PavlenkoG/ECP5_PCIE_Analyzer/fpga_logic/src/pcs_pci_rx.vhd

--
-- Verific VHDL Description of module DCUA
--

-- DCUA is a black-box. Cannot print a valid VHDL entity description for it

--
-- Verific VHDL Description of module pcs_pci_rx
--

library ieee ;
use ieee.std_logic_1164.all ;

library ecp5um ;
use ecp5um.components.all ;

entity pcs_pci_rx is
    port (hdinp: in std_logic;
        hdinn: in std_logic;
        rxrefclk: in std_logic;
        rx_pclk: out std_logic;
        rxdata: out std_logic_vector(7 downto 0);
        rx_k: out std_logic_vector(0 downto 0);
        rxstatus0: out std_logic_vector(2 downto 0);
        pcie_det_en_c: in std_logic;
        pcie_ct_c: in std_logic;
        signal_detect_c: in std_logic;
        pcie_done_s: out std_logic;
        pcie_con_s: out std_logic;
        rx_los_low_s: out std_logic;
        lsm_status_s: out std_logic;
        rx_cdr_lol_s: out std_logic;
        rx_pcs_rst_c: in std_logic;
        rx_serdes_rst_c: in std_logic;
        rx_pwrup_c: in std_logic;
        rst_dual_c: in std_logic;
        serdes_rst_dual_c: in std_logic;
        serdes_pdb: in std_logic
    );
    
end entity pcs_pci_rx;

architecture v1 of pcs_pci_rx is 
    signal n40,n39,n1,n2,n3,n4,rx_pclk_c,n5,n6,n7,n8,n9,n10,n11,
        n12,n13,n14,n15,n16,n17,n18,n19,n20,n21,n22,n23,n24,n25,
        n26,n27,n28,n29,n30,n31,n32,n33,n34,n35,n36,n37,n38,n41,
        gnd,pwr,n42,n43,n44,n45,n46,n47,n48,n49,n50,n51,n52,n53,
        n54,n55,n56,n57,n58,n59,n60,n61,n62,n63,n64,n65,n66,n67,
        n68,n69,n70,n71,n72,n73,n74,n75,n76,n77,n78,n79,n80,n81,
        n82,n83,n84,n85,n86,n87,n88,n89,n90,n91,n92,n93,n94,n95,
        n96,n97,n98,n99,n100,n101,n102,n103,n104,n105,n106,n107,
        n108,n109,n110,n111,n112,n113,\_Z\ : std_logic; 
    attribute LOC : string;
    attribute LOC of DCU1_inst : label is "DCU1";
    attribute CHAN : string;
    attribute CHAN of DCU1_inst : label is "CH0";
begin
    rx_pclk <= rx_pclk_c;
    DCU1_inst: component DCUA generic map (D_MACROPDB=>"0b1",D_IB_PWDNB=>"0b1",
        D_XGE_MODE=>"0b0",D_LOW_MARK=>"0d4",D_HIGH_MARK=>"0d12",D_BUS8BIT_SEL=>"0b0",
        D_CDR_LOL_SET=>"0b00",D_TXPLL_PWDNB=>"0b1",CH0_UC_MODE=>"0b0",CH0_PCIE_MODE=>"0b1",
        CH0_RIO_MODE=>"0b0",CH0_WA_MODE=>"0b0",CH0_INVERT_RX=>"0b1",CH0_INVERT_TX=>"0b0",
        CH0_PRBS_SELECTION=>"0b0",CH0_GE_AN_ENABLE=>"0b0",CH0_PRBS_LOCK=>"0b0",
        CH0_PRBS_ENABLE=>"0b0",CH0_ENABLE_CG_ALIGN=>"0b1",CH0_TX_GEAR_MODE=>"0b1",
        CH0_RX_GEAR_MODE=>"0b0",CH0_PCS_DET_TIME_SEL=>"0b00",CH0_PCIE_EI_EN=>"0b0",
        CH0_TX_GEAR_BYPASS=>"0b0",CH0_ENC_BYPASS=>"0b0",CH0_SB_BYPASS=>"0b0",
        CH0_RX_SB_BYPASS=>"0b1",CH0_WA_BYPASS=>"0b0",CH0_DEC_BYPASS=>"0b0",
        CH0_CTC_BYPASS=>"0b1",CH0_RX_GEAR_BYPASS=>"0b0",CH0_LSM_DISABLE=>"0b0",
        CH0_MATCH_2_ENABLE=>"0b0",CH0_MATCH_4_ENABLE=>"0b1",CH0_MIN_IPG_CNT=>"0b11",
        CH0_CC_MATCH_1=>"0x1BC",CH0_CC_MATCH_2=>"0x11C",CH0_CC_MATCH_3=>"0x11C",
        CH0_CC_MATCH_4=>"0x11C",CH0_UDF_COMMA_MASK=>"0x3ff",CH0_UDF_COMMA_A=>"0x283",
        CH0_UDF_COMMA_B=>"0x17C",CH0_RX_DCO_CK_DIV=>"0b000",CH0_RCV_DCC_EN=>"0b0",
        CH0_TPWDNB=>"0b0",CH0_RATE_MODE_TX=>"0b0",CH0_RTERM_TX=>"0d19",CH0_TX_CM_SEL=>"0b00",
        CH0_TDRV_PRE_EN=>"0b0",CH0_TDRV_SLICE0_SEL=>"0b00",CH0_TDRV_SLICE1_SEL=>"0b00",
        CH0_TDRV_SLICE2_SEL=>"0b00",CH0_TDRV_SLICE3_SEL=>"0b00",CH0_TDRV_SLICE4_SEL=>"0b00",
        CH0_TDRV_SLICE5_SEL=>"0b00",CH0_TDRV_SLICE0_CUR=>"0b000",CH0_TDRV_SLICE1_CUR=>"0b000",
        CH0_TDRV_SLICE2_CUR=>"0b00",CH0_TDRV_SLICE3_CUR=>"0b00",CH0_TDRV_SLICE4_CUR=>"0b00",
        CH0_TDRV_SLICE5_CUR=>"0b00",CH0_TDRV_DAT_SEL=>"0b00",CH0_TX_DIV11_SEL=>"0b0",
        CH0_RPWDNB=>"0b1",CH0_RATE_MODE_RX=>"0b0",CH0_RX_DIV11_SEL=>"0b0",
        CH0_SEL_SD_RX_CLK=>"0b1",CH0_FF_RX_H_CLK_EN=>"0b0",CH0_FF_RX_F_CLK_DIS=>"0b0",
        CH0_FF_TX_H_CLK_EN=>"0b1",CH0_FF_TX_F_CLK_DIS=>"0b1",CH0_TDRV_POST_EN=>"0b0",
        CH0_TX_POST_SIGN=>"0b0",CH0_TX_PRE_SIGN=>"0b0",CH0_REQ_LVL_SET=>"0b00",
        CH0_REQ_EN=>"0b0",CH0_RTERM_RX=>"0d22",CH0_RXTERM_CM=>"0b11",CH0_PDEN_SEL=>"0b1",
        CH0_RXIN_CM=>"0b11",CH0_LEQ_OFFSET_SEL=>"0b0",CH0_LEQ_OFFSET_TRIM=>"0b000",
        CH0_RLOS_SEL=>"0b1",CH0_RX_LOS_LVL=>"0b100",CH0_RX_LOS_CEQ=>"0b11",
        CH0_RX_LOS_HYST_EN=>"0b0",CH0_RX_LOS_EN=>"0b1",CH0_LDR_RX2CORE_SEL=>"0b0",
        CH0_LDR_CORE2TX_SEL=>"0b0",D_TX_MAX_RATE=>"5",CH0_CDR_MAX_RATE=>"2.5",
        CH0_TXAMPLITUDE=>"0d880",CH0_TXDEPRE=>"DISABLED",CH0_TXDEPOST=>"DISABLED",
        CH0_PROTOCOL=>"PCIE",D_ISETLOS=>"0d0",D_SETIRPOLY_AUX=>"0b00",D_SETICONST_AUX=>"0b00",
        D_SETIRPOLY_CH=>"0b00",D_SETICONST_CH=>"0b00",D_REQ_ISET=>"0b000",
        D_PD_ISET=>"0b00",D_DCO_CALIB_TIME_SEL=>"0b00",CH0_CDR_CNT4SEL=>"0b00",
        CH0_CDR_CNT8SEL=>"0b00",CH0_DCOATDCFG=>"0b00",CH0_DCOATDDLY=>"0b00",
        CH0_DCOBYPSATD=>"0b1",CH0_DCOCALDIV=>"0b001",CH0_DCOCTLGI=>"0b010",
        CH0_DCODISBDAVOID=>"0b0",CH0_DCOFLTDAC=>"0b01",CH0_DCOFTNRG=>"0b111",
        CH0_DCOIOSTUNE=>"0b000",CH0_DCOITUNE=>"0b00",CH0_DCOITUNE4LSB=>"0b111",
        CH0_DCOIUPDNX2=>"0b1",CH0_DCONUOFLSB=>"0b101",CH0_DCOSCALEI=>"0b00",
        CH0_DCOSTARTVAL=>"0b000",CH0_DCOSTEP=>"0b00",CH0_BAND_THRESHOLD=>"0d0",
        CH0_AUTO_FACQ_EN=>"0b1",CH0_AUTO_CALIB_EN=>"0b1",CH0_CALIB_CK_MODE=>"0b0",
        CH0_REG_BAND_OFFSET=>"0d0",CH0_REG_BAND_SEL=>"0d0",CH0_REG_IDAC_SEL=>"0d0",
        CH0_REG_IDAC_EN=>"0b0",D_CMUSETISCL4VCO=>"0b000",D_CMUSETI4VCO=>"0b00",
        D_CMUSETINITVCT=>"0b00",D_CMUSETZGM=>"0b000",D_CMUSETP2AGM=>"0b000",
        D_CMUSETP1GM=>"0b000",D_CMUSETI4CPZ=>"0d3",D_CMUSETI4CPP=>"0d3",D_CMUSETICP4Z=>"0b101",
        D_CMUSETICP4P=>"0b01",D_CMUSETBIASI=>"0b00",CH0_RX_RATE_SEL=>"0d8")
     port map (CH0_HDINP=>hdinp,CH1_HDINP=>gnd,CH0_HDINN=>hdinn,CH1_HDINN=>gnd,
    D_TXBIT_CLKP_FROM_ND=>n39,D_TXBIT_CLKN_FROM_ND=>n39,D_SYNC_ND=>n39,D_TXPLL_LOL_FROM_ND=>n39,
    CH0_RX_REFCLK=>rxrefclk,CH1_RX_REFCLK=>gnd,CH0_FF_RXI_CLK=>rx_pclk_c,
    CH1_FF_RXI_CLK=>pwr,CH0_FF_TXI_CLK=>n40,CH1_FF_TXI_CLK=>pwr,CH0_FF_EBRD_CLK=>n40,
    CH1_FF_EBRD_CLK=>pwr,CH0_FF_TX_D_0=>gnd,CH1_FF_TX_D_0=>gnd,CH0_FF_TX_D_1=>gnd,
    CH1_FF_TX_D_1=>gnd,CH0_FF_TX_D_2=>gnd,CH1_FF_TX_D_2=>gnd,CH0_FF_TX_D_3=>gnd,
    CH1_FF_TX_D_3=>gnd,CH0_FF_TX_D_4=>gnd,CH1_FF_TX_D_4=>gnd,CH0_FF_TX_D_5=>gnd,
    CH1_FF_TX_D_5=>gnd,CH0_FF_TX_D_6=>gnd,CH1_FF_TX_D_6=>gnd,CH0_FF_TX_D_7=>gnd,
    CH1_FF_TX_D_7=>gnd,CH0_FF_TX_D_8=>gnd,CH1_FF_TX_D_8=>gnd,CH0_FF_TX_D_9=>gnd,
    CH1_FF_TX_D_9=>gnd,CH0_FF_TX_D_10=>gnd,CH1_FF_TX_D_10=>gnd,CH0_FF_TX_D_11=>gnd,
    CH1_FF_TX_D_11=>gnd,CH0_FF_TX_D_12=>gnd,CH1_FF_TX_D_12=>gnd,CH0_FF_TX_D_13=>gnd,
    CH1_FF_TX_D_13=>gnd,CH0_FF_TX_D_14=>gnd,CH1_FF_TX_D_14=>gnd,CH0_FF_TX_D_15=>gnd,
    CH1_FF_TX_D_15=>gnd,CH0_FF_TX_D_16=>gnd,CH1_FF_TX_D_16=>gnd,CH0_FF_TX_D_17=>gnd,
    CH1_FF_TX_D_17=>gnd,CH0_FF_TX_D_18=>gnd,CH1_FF_TX_D_18=>gnd,CH0_FF_TX_D_19=>gnd,
    CH1_FF_TX_D_19=>gnd,CH0_FF_TX_D_20=>gnd,CH1_FF_TX_D_20=>gnd,CH0_FF_TX_D_21=>gnd,
    CH1_FF_TX_D_21=>gnd,CH0_FF_TX_D_22=>gnd,CH1_FF_TX_D_22=>gnd,CH0_FF_TX_D_23=>gnd,
    CH1_FF_TX_D_23=>gnd,CH0_FFC_EI_EN=>gnd,CH1_FFC_EI_EN=>gnd,CH0_FFC_PCIE_DET_EN=>pcie_det_en_c,
    CH1_FFC_PCIE_DET_EN=>gnd,CH0_FFC_PCIE_CT=>pcie_ct_c,CH1_FFC_PCIE_CT=>gnd,
    CH0_FFC_SB_INV_RX=>gnd,CH1_FFC_SB_INV_RX=>gnd,CH0_FFC_ENABLE_CGALIGN=>gnd,
    CH1_FFC_ENABLE_CGALIGN=>gnd,CH0_FFC_SIGNAL_DETECT=>signal_detect_c,CH1_FFC_SIGNAL_DETECT=>gnd,
    CH0_FFC_FB_LOOPBACK=>gnd,CH1_FFC_FB_LOOPBACK=>gnd,CH0_FFC_SB_PFIFO_LP=>n39,
    CH1_FFC_SB_PFIFO_LP=>gnd,CH0_FFC_PFIFO_CLR=>n39,CH1_FFC_PFIFO_CLR=>gnd,
    CH0_FFC_RATE_MODE_RX=>n39,CH1_FFC_RATE_MODE_RX=>gnd,CH0_FFC_RATE_MODE_TX=>n39,
    CH1_FFC_RATE_MODE_TX=>gnd,CH0_FFC_DIV11_MODE_RX=>n39,CH1_FFC_DIV11_MODE_RX=>gnd,
    CH0_FFC_DIV11_MODE_TX=>n39,CH1_FFC_DIV11_MODE_TX=>gnd,CH0_FFC_RX_GEAR_MODE=>n39,
    CH1_FFC_RX_GEAR_MODE=>gnd,CH0_FFC_TX_GEAR_MODE=>n39,CH1_FFC_TX_GEAR_MODE=>gnd,
    CH0_FFC_LDR_CORE2TX_EN=>gnd,CH1_FFC_LDR_CORE2TX_EN=>gnd,CH0_FFC_LANE_TX_RST=>gnd,
    CH1_FFC_LANE_TX_RST=>gnd,CH0_FFC_LANE_RX_RST=>rx_pcs_rst_c,CH1_FFC_LANE_RX_RST=>gnd,
    CH0_FFC_RRST=>rx_serdes_rst_c,CH1_FFC_RRST=>gnd,CH0_FFC_TXPWDNB=>gnd,
    CH1_FFC_TXPWDNB=>gnd,CH0_FFC_RXPWDNB=>rx_pwrup_c,CH1_FFC_RXPWDNB=>gnd,
    CH0_LDR_CORE2TX=>gnd,CH1_LDR_CORE2TX=>gnd,D_SCIWDATA0=>gnd,D_SCIWDATA1=>gnd,
    D_SCIWDATA2=>gnd,D_SCIWDATA3=>gnd,D_SCIWDATA4=>gnd,D_SCIWDATA5=>gnd,
    D_SCIWDATA6=>gnd,D_SCIWDATA7=>gnd,D_SCIADDR0=>gnd,D_SCIADDR1=>gnd,D_SCIADDR2=>gnd,
    D_SCIADDR3=>gnd,D_SCIADDR4=>gnd,D_SCIADDR5=>gnd,D_SCIENAUX=>gnd,D_SCISELAUX=>gnd,
    CH0_SCIEN=>gnd,CH1_SCIEN=>gnd,CH0_SCISEL=>gnd,CH1_SCISEL=>gnd,D_SCIRD=>gnd,
    D_SCIWSTN=>gnd,D_CYAWSTN=>gnd,D_FFC_SYNC_TOGGLE=>gnd,D_FFC_DUAL_RST=>rst_dual_c,
    D_FFC_MACRO_RST=>serdes_rst_dual_c,D_FFC_MACROPDB=>serdes_pdb,D_FFC_TRST=>n40,
    CH0_FFC_CDR_EN_BITSLIP=>n39,CH1_FFC_CDR_EN_BITSLIP=>gnd,D_SCAN_ENABLE=>n39,
    D_SCAN_IN_0=>n39,D_SCAN_IN_1=>n39,D_SCAN_IN_2=>n39,D_SCAN_IN_3=>n39,
    D_SCAN_IN_4=>n39,D_SCAN_IN_5=>n39,D_SCAN_IN_6=>n39,D_SCAN_IN_7=>n39,
    D_SCAN_MODE=>n39,D_SCAN_RESET=>n39,D_CIN0=>n39,D_CIN1=>n39,D_CIN2=>n39,
    D_CIN3=>n39,D_CIN4=>n39,D_CIN5=>n39,D_CIN6=>n39,D_CIN7=>n39,D_CIN8=>n39,
    D_CIN9=>n39,D_CIN10=>n39,D_CIN11=>n39,CH0_HDOUTP=>n42,CH1_HDOUTP=>n43,
    CH0_HDOUTN=>n44,CH1_HDOUTN=>n45,D_TXBIT_CLKP_TO_ND=>n1,D_TXBIT_CLKN_TO_ND=>n2,
    D_SYNC_PULSE2ND=>n3,D_TXPLL_LOL_TO_ND=>n4,CH0_FF_RX_F_CLK=>n5,CH1_FF_RX_F_CLK=>n46,
    CH0_FF_RX_H_CLK=>n6,CH1_FF_RX_H_CLK=>n47,CH0_FF_TX_F_CLK=>n7,CH1_FF_TX_F_CLK=>n48,
    CH0_FF_TX_H_CLK=>n8,CH1_FF_TX_H_CLK=>n49,CH0_FF_RX_PCLK=>rx_pclk_c,CH1_FF_RX_PCLK=>n50,
    CH0_FF_TX_PCLK=>n51,CH1_FF_TX_PCLK=>n52,CH0_FF_RX_D_0=>rxdata(0),CH1_FF_RX_D_0=>n53,
    CH0_FF_RX_D_1=>rxdata(1),CH1_FF_RX_D_1=>n54,CH0_FF_RX_D_2=>rxdata(2),
    CH1_FF_RX_D_2=>n55,CH0_FF_RX_D_3=>rxdata(3),CH1_FF_RX_D_3=>n56,CH0_FF_RX_D_4=>rxdata(4),
    CH1_FF_RX_D_4=>n57,CH0_FF_RX_D_5=>rxdata(5),CH1_FF_RX_D_5=>n58,CH0_FF_RX_D_6=>rxdata(6),
    CH1_FF_RX_D_6=>n59,CH0_FF_RX_D_7=>rxdata(7),CH1_FF_RX_D_7=>n60,CH0_FF_RX_D_8=>rx_k(0),
    CH1_FF_RX_D_8=>n61,CH0_FF_RX_D_9=>rxstatus0(0),CH1_FF_RX_D_9=>n62,CH0_FF_RX_D_10=>rxstatus0(1),
    CH1_FF_RX_D_10=>n63,CH0_FF_RX_D_11=>rxstatus0(2),CH1_FF_RX_D_11=>n64,
    CH0_FF_RX_D_12=>n65,CH1_FF_RX_D_12=>n66,CH0_FF_RX_D_13=>n67,CH1_FF_RX_D_13=>n68,
    CH0_FF_RX_D_14=>n69,CH1_FF_RX_D_14=>n70,CH0_FF_RX_D_15=>n71,CH1_FF_RX_D_15=>n72,
    CH0_FF_RX_D_16=>n73,CH1_FF_RX_D_16=>n74,CH0_FF_RX_D_17=>n75,CH1_FF_RX_D_17=>n76,
    CH0_FF_RX_D_18=>n77,CH1_FF_RX_D_18=>n78,CH0_FF_RX_D_19=>n79,CH1_FF_RX_D_19=>n80,
    CH0_FF_RX_D_20=>n81,CH1_FF_RX_D_20=>n82,CH0_FF_RX_D_21=>n83,CH1_FF_RX_D_21=>n84,
    CH0_FF_RX_D_22=>n85,CH1_FF_RX_D_22=>n86,CH0_FF_RX_D_23=>n87,CH1_FF_RX_D_23=>n88,
    CH0_FFS_PCIE_DONE=>pcie_done_s,CH1_FFS_PCIE_DONE=>n89,CH0_FFS_PCIE_CON=>pcie_con_s,
    CH1_FFS_PCIE_CON=>n90,CH0_FFS_RLOS=>rx_los_low_s,CH1_FFS_RLOS=>n91,CH0_FFS_LS_SYNC_STATUS=>lsm_status_s,
    CH1_FFS_LS_SYNC_STATUS=>n92,CH0_FFS_CC_UNDERRUN=>n93,CH1_FFS_CC_UNDERRUN=>n94,
    CH0_FFS_CC_OVERRUN=>n95,CH1_FFS_CC_OVERRUN=>n96,CH0_FFS_RXFBFIFO_ERROR=>n9,
    CH1_FFS_RXFBFIFO_ERROR=>n97,CH0_FFS_TXFBFIFO_ERROR=>n10,CH1_FFS_TXFBFIFO_ERROR=>n98,
    CH0_FFS_RLOL=>rx_cdr_lol_s,CH1_FFS_RLOL=>n99,CH0_FFS_SKP_ADDED=>n100,
    CH1_FFS_SKP_ADDED=>n101,CH0_FFS_SKP_DELETED=>n102,CH1_FFS_SKP_DELETED=>n103,
    CH0_LDR_RX2CORE=>n104,CH1_LDR_RX2CORE=>n105,D_SCIRDATA0=>n106,D_SCIRDATA1=>n107,
    D_SCIRDATA2=>n108,D_SCIRDATA3=>n109,D_SCIRDATA4=>n110,D_SCIRDATA5=>n111,
    D_SCIRDATA6=>n112,D_SCIRDATA7=>n113,D_SCIINT=>\_Z\,D_SCAN_OUT_0=>n11,
    D_SCAN_OUT_1=>n12,D_SCAN_OUT_2=>n13,D_SCAN_OUT_3=>n14,D_SCAN_OUT_4=>n15,
    D_SCAN_OUT_5=>n16,D_SCAN_OUT_6=>n17,D_SCAN_OUT_7=>n18,D_COUT0=>n19,D_COUT1=>n20,
    D_COUT2=>n21,D_COUT3=>n22,D_COUT4=>n23,D_COUT5=>n24,D_COUT6=>n25,D_COUT7=>n26,
    D_COUT8=>n27,D_COUT9=>n28,D_COUT10=>n29,D_COUT11=>n30,D_COUT12=>n31,
    D_COUT13=>n32,D_COUT14=>n33,D_COUT15=>n34,D_COUT16=>n35,D_COUT17=>n36,
    D_COUT18=>n37,D_COUT19=>n38,D_REFCLKI=>gnd,D_FFS_PLOL=>n41);
    n40 <= '1' ;
    n39 <= '0' ;
    n1 <= 'Z' ;
    n2 <= 'Z' ;
    n3 <= 'Z' ;
    n4 <= 'Z' ;
    n5 <= 'Z' ;
    n6 <= 'Z' ;
    n7 <= 'Z' ;
    n8 <= 'Z' ;
    n9 <= 'Z' ;
    n10 <= 'Z' ;
    n11 <= 'Z' ;
    n12 <= 'Z' ;
    n13 <= 'Z' ;
    n14 <= 'Z' ;
    n15 <= 'Z' ;
    n16 <= 'Z' ;
    n17 <= 'Z' ;
    n18 <= 'Z' ;
    n19 <= 'Z' ;
    n20 <= 'Z' ;
    n21 <= 'Z' ;
    n22 <= 'Z' ;
    n23 <= 'Z' ;
    n24 <= 'Z' ;
    n25 <= 'Z' ;
    n26 <= 'Z' ;
    n27 <= 'Z' ;
    n28 <= 'Z' ;
    n29 <= 'Z' ;
    n30 <= 'Z' ;
    n31 <= 'Z' ;
    n32 <= 'Z' ;
    n33 <= 'Z' ;
    n34 <= 'Z' ;
    n35 <= 'Z' ;
    n36 <= 'Z' ;
    n37 <= 'Z' ;
    n38 <= 'Z' ;
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
    gnd <= '0' ;
    pwr <= '1' ;
    n42 <= 'Z' ;
    n43 <= 'Z' ;
    n44 <= 'Z' ;
    n45 <= 'Z' ;
    n46 <= 'Z' ;
    n47 <= 'Z' ;
    n48 <= 'Z' ;
    n49 <= 'Z' ;
    n50 <= 'Z' ;
    n51 <= 'Z' ;
    n52 <= 'Z' ;
    n53 <= 'Z' ;
    n54 <= 'Z' ;
    n55 <= 'Z' ;
    n56 <= 'Z' ;
    n57 <= 'Z' ;
    n58 <= 'Z' ;
    n59 <= 'Z' ;
    n60 <= 'Z' ;
    n61 <= 'Z' ;
    n62 <= 'Z' ;
    n63 <= 'Z' ;
    n64 <= 'Z' ;
    n65 <= 'Z' ;
    n66 <= 'Z' ;
    n67 <= 'Z' ;
    n68 <= 'Z' ;
    n69 <= 'Z' ;
    n70 <= 'Z' ;
    n71 <= 'Z' ;
    n72 <= 'Z' ;
    n73 <= 'Z' ;
    n74 <= 'Z' ;
    n75 <= 'Z' ;
    n76 <= 'Z' ;
    n77 <= 'Z' ;
    n78 <= 'Z' ;
    n79 <= 'Z' ;
    n80 <= 'Z' ;
    n81 <= 'Z' ;
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
    \_Z\ <= 'Z' ;
    
end architecture v1;
