PavlenkoG/ECP5_PCIE_Analyzer/fpga_logic/sim/vunit/analyzer_tb_pkg.vhd

library ieee;
use ieee.std_logic_1164.all;
use ieee.std_logic_unsigned.all;
use ieee.numeric_std.all;
use ieee.std_logic_textio.all;
use std.textio.all;
use ieee.math_real.all;

use work.pcie_tx_engine_pkg.all;
use work.pci_wrapper_pkg.all;
use work.top_pkg.all;

package analyzer_tb_pkg is

    constant C_PACKET_LEN         : integer := 24;
    constant C_TEST_LEN           : integer := 50;
    constant C_MODULE_IN_TEST     : std_logic_vector (31 downto 0) := X"FFFFFFFF";
    constant FH_TRAFFIC_GENERATOR : boolean := false;
    constant TEST_MODUL_GENERATE  : boolean := false;

    -- type to store memory read tlp requestions
    type t_read_mem is record
        requester_id    : std_logic_vector (15 downto 0);
        tag             : std_logic_vector (7 downto 0);
        dw              : std_logic_vector (7 downto 0);
        length          : std_logic_vector (9 downto 0);
        address         : std_logic_vector (31 downto 0);
        ena             : boolean;
        tlp_type        : std_logic_vector(6 downto 0);
    end record;

    -- array to store memory read tlp requestions
    type t_read_mem_arr is array (0 to 32) of t_read_mem;

    -- array event index
    type t_tx_evt_idx is array (0 to 31) of std_logic_vector (1 downto 0);

    -- this function converts string to std_logic_vector (32 downto 0)
    -- or std_logic_vector (15 downto 0) or std_logic_vector (7 downto 0)
    -- string as input (8,4 or 2 character)
    function x_read_f (s : string)return STD_LOGIC_VECTOR;
    -- this function calculates FirstDW and LastDW fields
    function dw_assign (addr : std_logic_vector(1 downto 0); len : integer) return std_logic_vector;
    -- this procedure prepares and send 3DW TLP Header
    procedure header_f (signal clk : in std_logic;
                        constant addr : in std_logic_vector(31 downto 0);
                        constant fmt : in std_logic_vector (6 downto 0);
                        constant len : in integer;
                        signal tlp_in : in t_tx_tlp_intf_q;
                        signal tlp_out : out t_tx_tlp_intf_d);
    -- this procedure handle ptm mechanism
    procedure ptm_handle (signal clk : in std_logic;
                        signal ptm_timer    : in std_logic_vector (63 downto 0);
                        signal requests : in t_read_mem;
                        signal tlp_in : in t_tx_tlp_intf_q;
                        signal tlp_out : out t_tx_tlp_intf_d);

    -- this procedure prepares and sends 3DW TLP Header for CplD packet
    procedure header_cpl (signal clk : in std_logic;
                          constant addr : in std_logic_vector (31 downto 0);
                          constant len : in integer;
                          constant req_id : std_logic_vector (15 downto 0);
                          constant dw : std_logic_vector (7 downto 0);
                          constant tag : std_logic_vector (7 downto 0);
                          signal tlp_in : in t_tx_tlp_intf_q;
                          signal tlp_out : out t_tx_tlp_intf_d);
    -- this procedure sends data payload
    type payload_t is array (0 to 128) of std_logic_vector (7 downto 0);

    -- interrupt counter to place in packet
    type interrupt_num_t is array(0 to 31) of std_logic_vector (7 downto 0);

    -- this procedure prepares tlp payload
    procedure payload_f (signal clk : in std_logic;
                         constant payload : in payload_t;
                         signal tlp_out : out t_tx_tlp_intf_d
                        );
    -- this procedure send burst of data
    procedure payload_brst_f (signal clk : in std_logic;
                         constant payload : in payload_t;
                         constant len : in integer;
                         signal tlp_out : out t_tx_tlp_intf_d
                        );
    -- this procedure send data to frame handler
    procedure fh_write (signal clk : in std_logic;
                        constant payload : in payload_t;
                        constant len : in integer;
                        constant modul_num : in integer;
                        signal tx_ready : in std_logic_vector (MODUL_NUM_CONST - 1 downto 0);
                        signal tx_valid : out std_logic_vector (MODUL_NUM_CONST - 1 downto 0);
                        signal tx_data : out std_logic_vector (7 downto 0);
                        signal tx_last : out std_logic_vector (MODUL_NUM_CONST - 1 downto 0)
                        );

    procedure w_pci (   signal clk          : in std_logic;
                        signal addr         : in std_logic_vector (31 downto 0);
                        signal len          : in integer;
                        signal payload      : in payload_t;
                        signal tlp_in       : in t_tx_tlp_intf_q;
                        signal tlp_out      : out t_tx_tlp_intf_d
                        );

    procedure spi_test (
                        constant freq       : in integer;
                        signal clk          : out std_logic;
                        signal miso         : in std_logic;
                        signal mosi         : out std_logic;
                        signal cs           : out std_logic;

                        signal data_in      : in payload_t;
                        signal data_out     : out payload_t;
                        constant len          : in integer
    );

end package;
package body analyzer_tb_pkg is
    -- array for x_read_f
    type indexed_char is array (0 to 15) of character;
    constant HEX_VALUE : indexed_char :=
                ('0','1','2','3','4','5','6','7','8','9','A','B','C','D','E','F');

--------------------------------------------------------------------------------
-- read hex string
--------------------------------------------------------------------------------
    function x_read_f (s: string) return std_logic_vector is
        variable k : integer;
        variable v : std_logic_vector ((s'high*4)-1 downto 0);
        variable r : integer;
    begin
        k:= s'high - s'low;
        r:= s'high*4-1;
        for i in 0 to k loop
            for j in 0 to 15 loop
                if (s(i+1)=HEX_VALUE(j)) then
                    v((r-i*4) downto ((r-3)-i*4)):= std_logic_vector (to_signed(j,4));
                end if;
            end loop;
        end loop;
        return v;
    end x_read_f;

--------------------------------------------------------------------------------
-- assign dw field
--------------------------------------------------------------------------------
    function dw_assign (addr : std_logic_vector(1 downto 0); len : integer) return std_logic_vector is
        variable dw : std_logic_vector (7 downto 0);
        variable len_temp : integer;
        variable i : integer;
    begin
        i := 0;
        dw := "00000000";
        len_temp := len;
        -- assign first dw
        len_1dw: loop
            if i >= addr then
                dw(i) := '1';
                len_temp := len_temp - 1;
            end if;
            if i = 3 or len_temp = 0 then
                i := i + 1;
                exit len_1dw;
            end if;
            i := i + 1;
        end loop;
        while len_temp > 4 loop
            len_temp := len_temp - 4;
        end loop;
        -- assign last dw
        len_2dw : loop
            if len_temp /= 0 then dw(i) := '1'; end if;
            if i = 7 or len_temp = 0 then
                exit len_2dw;
            end if;
            len_temp := len_temp - 1;
            i := i + 1;
        end loop;
        return dw;
    end dw_assign;

--------------------------------------------------------------------------------
-- write tlp header
--------------------------------------------------------------------------------
    procedure header_f (signal clk : in std_logic;
                        constant addr : in std_logic_vector(31 downto 0);
                        constant fmt : in std_logic_vector (6 downto 0);
                        constant len : in integer;
                        signal tlp_in : in t_tx_tlp_intf_q;
                        signal tlp_out : out t_tx_tlp_intf_d) is
    begin
        -- set request signal
        tlp_out.tx_data_vc0 <= (others => '0');
        tlp_out.tx_st_vc0 <= '0';
        tlp_out.tx_end_vc0 <= '0';
        wait until clk = '1';
        tlp_out.tx_req_vc0 <= '1';
        -- wait for ready to send
        wait until tlp_in.tx_rdy_vc0 = '1';
        wait until clk = '1';
        tlp_out.tx_req_vc0 <= '0';
        -- set start and send packet format
        wait until clk = '1';
        tlp_out.tx_st_vc0 <= '1';
        tlp_out.tx_data_vc0(15) <= '0';
        tlp_out.tx_data_vc0(14 downto 8) <= fmt;
        tlp_out.tx_data_vc0(7 downto 0) <= (others => '0');
        wait until clk = '1';
        -- send length of packet
        tlp_out.tx_st_vc0 <= '0';
        tlp_out.tx_req_vc0 <= '0';
        if len >= 4 then tlp_out.tx_data_vc0(9 downto 0) <= std_logic_vector (to_signed(((len-1)/4)+1,10)) ; end if;
        if len < 4 then
            tlp_out.tx_data_vc0(9 downto 0) <= len_calc(addr(1 downto 0), (std_logic_vector(to_signed(len,7))));
        end if;
        tlp_out.tx_data_vc0(15 downto 10) <= (others => '0');
        wait until clk = '1';
        -- send requester id
        tlp_out.tx_data_vc0 <= (others => '0');
        wait until clk = '1';
        -- send tag and FirstDW/LastDW
        tlp_out.tx_data_vc0(15 downto 8) <= X"54"; --(others => '0');
        tlp_out.tx_data_vc0(7 downto 0) <= dw_assign (addr(1 downto 0), len);
        ------------------------------------------------------------------------
        ------------------------------------------------------------------------
        wait until clk = '1';
        -- send address
        tlp_out.tx_data_vc0(15 downto 0) <= addr (31 downto 16);
        wait until clk = '1';
        tlp_out.tx_data_vc0(15 downto 0) <= addr(15 downto 2) & "00";
        if fmt = RX_MEM_RD_FMT_TYPE or fmt = RX_CFG_RD_FMT_TYPE then
            tlp_out.tx_end_vc0 <= '1';
        end if;
        wait until clk = '1';
        tlp_out.tx_end_vc0 <= '0';
    end header_f;

    procedure header_cpl (signal clk : in std_logic;
                          constant addr : in std_logic_vector (31 downto 0);
                          constant len : in integer;
                          constant req_id : std_logic_vector (15 downto 0);
                          constant dw : std_logic_vector (7 downto 0);
                          constant tag : std_logic_vector (7 downto 0);
                          signal tlp_in : in t_tx_tlp_intf_q;
                          signal tlp_out : out t_tx_tlp_intf_d) is
    begin
        -- set request signal
        tlp_out.tx_data_vc0 <= (others => '0');
        tlp_out.tx_st_vc0 <= '0';
        tlp_out.tx_end_vc0 <= '0';
        wait until clk = '1';
        tlp_out.tx_req_vc0 <= '1';
        -- wait for ready to send
        wait until tlp_in.tx_rdy_vc0 = '1';
        tlp_out.tx_req_vc0 <= '0';
        -- set start and send packet format
        tlp_out.tx_st_vc0 <= '1';
        tlp_out.tx_data_vc0(15) <= '0';
        tlp_out.tx_data_vc0(14 downto 8) <= RX_CPLD_FMT_TYPE;
        tlp_out.tx_data_vc0(7 downto 0) <= (others => '0');
        wait until clk = '1';
        -- send length of packet
        tlp_out.tx_st_vc0 <= '0';
        tlp_out.tx_req_vc0 <= '0';
        tlp_out.tx_data_vc0(9 downto 0) <=  std_logic_vector (to_signed(len,10));
        tlp_out.tx_data_vc0(15 downto 10) <= (others => '0');
        wait until clk = '1';
        -- send completer id
        tlp_out.tx_data_vc0 <= (others => '0');
        wait until clk = '1';
        -- send Cmpl Stauts and Byte count
        tlp_out.tx_data_vc0(15 downto 13) <= (others => '0');
--      tlp_out.tx_data_vc0(15 downto 13) <= "100";
            case dw is
                when "00001111" => tlp_out.tx_data_vc0(10 downto 0) <= "000" & X"04";
                when "00000111" => tlp_out.tx_data_vc0(10 downto 0) <= "000" & X"03";
                when "00001110" => tlp_out.tx_data_vc0(10 downto 0) <= "000" & X"03";
                when "00000011" => tlp_out.tx_data_vc0(10 downto 0) <= "000" & X"02";
                when "00000110" => tlp_out.tx_data_vc0(10 downto 0) <= "000" & X"02";
                when "00001100" => tlp_out.tx_data_vc0(10 downto 0) <= "000" & X"02";
                when "00000001" => tlp_out.tx_data_vc0(10 downto 0) <= "000" & X"01";
                when "00000010" => tlp_out.tx_data_vc0(10 downto 0) <= "000" & X"01";
                when "00000100" => tlp_out.tx_data_vc0(10 downto 0) <= "000" & X"01";
                when "00001000" => tlp_out.tx_data_vc0(10 downto 0) <= "000" & X"01";
                when "00000000" => tlp_out.tx_data_vc0(10 downto 0) <= "000" & X"01";
                when "11111111" => tlp_out.tx_data_vc0(10 downto 0) <= std_logic_vector(to_signed(len *4,11));
                when "01111111" => tlp_out.tx_data_vc0(10 downto 0) <= std_logic_vector(to_signed(len *4,11)) - 1;
                when "00111111" => tlp_out.tx_data_vc0(10 downto 0) <= std_logic_vector(to_signed(len *4,11)) - 2;
                when "00011111" => tlp_out.tx_data_vc0(10 downto 0) <= std_logic_vector(to_signed(len *4,11)) - 3;
                when "11111110" => tlp_out.tx_data_vc0(10 downto 0) <= std_logic_vector(to_signed(len *4,11)) - 1;
                when "01111110" => tlp_out.tx_data_vc0(10 downto 0) <= std_logic_vector(to_signed(len *4,11)) - 2;
                when "00111110" => tlp_out.tx_data_vc0(10 downto 0) <= std_logic_vector(to_signed(len *4,11)) - 3;
                when "00011110" => tlp_out.tx_data_vc0(10 downto 0) <= std_logic_vector(to_signed(len *4,11)) - 4;
                when "11111100" => tlp_out.tx_data_vc0(10 downto 0) <= std_logic_vector(to_signed(len *4,11)) - 2;
                when "01111100" => tlp_out.tx_data_vc0(10 downto 0) <= std_logic_vector(to_signed(len *4,11)) - 3;
                when "00111100" => tlp_out.tx_data_vc0(10 downto 0) <= std_logic_vector(to_signed(len *4,11)) - 4;
                when "00011100" => tlp_out.tx_data_vc0(10 downto 0) <= std_logic_vector(to_signed(len *4,11)) - 5;
                when "11111000" => tlp_out.tx_data_vc0(10 downto 0) <= std_logic_vector(to_signed(len *4,11)) - 3;
                when "01111000" => tlp_out.tx_data_vc0(10 downto 0) <= std_logic_vector(to_signed(len *4,11)) - 4;
                when "00111000" => tlp_out.tx_data_vc0(10 downto 0) <= std_logic_vector(to_signed(len *4,11)) - 5;
                when "00011000" => tlp_out.tx_data_vc0(10 downto 0) <= std_logic_vector(to_signed(len *4,11)) - 6;
                when others =>  tlp_out.tx_data_vc0(10 downto 0) <= (others => '0');
            end case;
        wait until clk = '1';
        -- send req_id
        tlp_out.tx_data_vc0(15 downto 0) <= req_id;
        wait until clk = '1';
        tlp_out.tx_data_vc0(15 downto 8) <= tag;
            if dw(3 downto 0) = "1111" or dw(3 downto 0) = "0111" or
               dw(3 downto 0) = "0011" or dw(3 downto 0) = "0001" then
                 tlp_out.tx_data_vc0(6 downto 0) <= (addr(6 downto 0));
            end if;
            if dw(3 downto 0) = "1110" or dw(3 downto 0) = "0110" or
               dw(3 downto 0) = "0010" then
                 tlp_out.tx_data_vc0(6 downto 0) <= (addr(6 downto 0)) + 1;
             end if;
             if dw(3 downto 0) = "1100" or dw(3 downto 0) = "0100" then
                 tlp_out.tx_data_vc0(6 downto 0) <= (addr(6 downto 0)) + 2;
             end if;
             if dw(3 downto 0) = "1000" then
                 tlp_out.tx_data_vc0(6 downto 0) <= (addr(6 downto 0)) + 3;
             end if;
--      tlp_out.tx_end_vc0 <= '1';
        wait until clk = '1';
        tlp_out.tx_end_vc0 <= '0';
    end header_cpl;


--------------------------------------------------------------------------------
-- write payload
--------------------------------------------------------------------------------

    procedure payload_f (signal clk : in std_logic;
                         constant payload : in payload_t;
                         signal tlp_out : out t_tx_tlp_intf_d
                        ) is
    begin
        tlp_out.tx_data_vc0(15 downto 8) <= payload(0);
        tlp_out.tx_data_vc0(7 downto 0) <= payload(1);
        wait until clk = '1';
        tlp_out.tx_end_vc0 <= '1';
        tlp_out.tx_data_vc0(15 downto 8) <= payload(2);
        tlp_out.tx_data_vc0(7 downto 0) <= payload(3);
        wait until clk = '1';
        tlp_out.tx_end_vc0 <= '0';
    end payload_f;

--------------------------------------------------------------------------------
-- write burst payload
--------------------------------------------------------------------------------

    procedure payload_brst_f (signal clk : in std_logic;
                         constant payload : in payload_t;
                         constant len : in integer;
                         signal tlp_out : out t_tx_tlp_intf_d
                        ) is
        variable counter : integer := 0;
    begin
        counter := 0;
        while counter /= len loop
            tlp_out.tx_data_vc0(15 downto 8) <= payload(counter + 0);
            tlp_out.tx_data_vc0(7 downto 0) <= payload(counter + 1);
            wait until clk = '1';
            if counter = len - 4 then
                tlp_out.tx_end_vc0 <= '1';
            end if;
            tlp_out.tx_data_vc0(15 downto 8) <= payload(counter + 2);
            tlp_out.tx_data_vc0(7 downto 0) <= payload(counter + 3);
            wait until clk = '1';
            counter := counter + 4;
        end loop;
        tlp_out.tx_end_vc0 <= '0';

    end payload_brst_f;

--------------------------------------------------------------------------------
-- write frame handler packet
--------------------------------------------------------------------------------
    procedure fh_write (signal clk : in std_logic;
                        constant payload : in payload_t;
                        constant len : in integer;
                        constant modul_num : in integer;
                        signal tx_ready : in std_logic_vector (MODUL_NUM_CONST - 1 downto 0);
                        signal tx_valid : out std_logic_vector (MODUL_NUM_CONST - 1 downto 0);
                        signal tx_data : out std_logic_vector (7 downto 0);
                        signal tx_last : out std_logic_vector (MODUL_NUM_CONST - 1 downto 0)
                        )is
        variable counter : integer := 0;
    begin
        wait until clk = '1';
        tx_valid <= (others => '0');
        tx_last <= (others => '0');
        tx_data <= (others => '0');
        if tx_ready(modul_num) = '0' then
            wait until tx_ready(modul_num) = '1';
        end if;
        wait until clk = '1';
        send: loop
            tx_valid(modul_num) <= '1';
            tx_data <= payload(counter);
            if counter = len-1 then
                tx_last(modul_num) <= '1';
                wait until clk = '1';
                tx_last(modul_num) <= '0';
                tx_valid(modul_num) <= '0';
                exit send;
            end if;
            if tx_ready(modul_num) = '1' then
                wait until clk = '1';
                counter := counter + 1;
            end if;
        end loop;
    end fh_write;

--------------------------------------------------------------------------------
-- ptm handle
--------------------------------------------------------------------------------
    procedure ptm_handle (signal clk : in std_logic;
                        signal ptm_timer    : in std_logic_vector (63 downto 0);
                        signal requests : in t_read_mem;
                        signal tlp_in : in t_tx_tlp_intf_q;
                        signal tlp_out : out t_tx_tlp_intf_d) is
        begin
        -- set request signal
        tlp_out.tx_data_vc0 <= (others => '0');
        tlp_out.tx_st_vc0 <= '0';
        tlp_out.tx_end_vc0 <= '0';
        wait until clk = '1';
        tlp_out.tx_req_vc0 <= '1';
        -- wait for ready to send
        wait until tlp_in.tx_rdy_vc0 = '1';
        tlp_out.tx_req_vc0 <= '0';
        -- set start and send packet format
        tlp_out.tx_st_vc0 <= '1';
        tlp_out.tx_data_vc0(15) <= '0';
        tlp_out.tx_data_vc0(14 downto 8) <= TX_MSG_RQ_FMT_TYPE;
        tlp_out.tx_data_vc0(7 downto 0) <= (others => '0');
        wait until clk = '1';
        -- send length of packet
        tlp_out.tx_st_vc0 <= '0';
        tlp_out.tx_req_vc0 <= '0';
        tlp_out.tx_data_vc0(15 downto 0) <= (others => '0');
        wait until clk = '1';
        -- send completer id
        tlp_out.tx_data_vc0 <= requests.requester_id;
        wait until clk = '1';
        tlp_out.tx_data_vc0(15 downto 0) <= X"00" & X"53";
        wait until clk = '1';
        wait until clk = '1';
        tlp_out.tx_end_vc0 <= '1';
        wait until clk = '1';
        tlp_out.tx_end_vc0 <= '0';

    end ptm_handle;

    procedure w_pci (
        signal clk          : in std_logic;
        signal addr         : in std_logic_vector (31 downto 0);
        signal len          : in integer;
        signal payload      : in payload_t;
        signal tlp_in       : in t_tx_tlp_intf_q;
        signal tlp_out      : out t_tx_tlp_intf_d) is
    begin
        header_f (clk, addr, RX_MEM_WR_FMT_TYPE, len, tlp_in, tlp_out);
        payload_brst_f (clk, payload, len, tlp_out);
    end w_pci;

    procedure spi_test (
                        constant freq       : in integer;
                        signal clk          : out std_logic;
                        signal miso         : in std_logic;
                        signal mosi         : out std_logic;
                        signal cs           : out std_logic;

                        signal data_in      : in payload_t;
                        signal data_out     : out payload_t;
                        constant len          : in integer) is
        variable f : real := Real(freq);
        variable wt : time := (1.0/f)/2.0 * 1 us;

    begin
        cs <= '0';
        wait for wt;-- (1/freq)*1 us;
        clk <= '0';
        for i in 0 to len - 1 loop
            for j in 0 to 7 loop
                data_out(i)(7 - j) <= miso;
                wait for wt;--(1/freq)*500 ns;
                clk <= '1';
                mosi <= data_in(i)(7 - j);
                wait for wt;--(1/freq)*500 ns;
                clk <= '0';
            end loop;
        end loop;
        wait for wt;-- (1/freq)*1 us;
        cs <= '1';
        wait for wt;--(1/freq)*1 us;
    end spi_test;

end package body;
